ayumu-bekki/B-Fox/bfox_receiver/main/logger.cc

// ESP32 B-Fox Receiver
// (C)2025 bekki.jp

// Include ----------------------
#include "logger.h"

namespace bfox_receiver_system {
namespace logger {

void InitializeLogLevel() {
#if CONFIG_DEBUG != 0
  esp_log_level_set("*", ESP_LOG_INFO);
  esp_log_level_set(kTag, ESP_LOG_VERBOSE);
  ESP_LOGD(kTag, "DEBUG MODE");
#else
  esp_log_level_set("*", ESP_LOG_WARN);
  esp_log_level_set(kTag, ESP_LOG_INFO);
#endif
}

}  // namespace logger
}  // namespace bfox_receiver_system
