ayumu-bekki/B-Fox/bfox_receiver/main/logger.h

#ifndef BFOX_RECEIVER_MAIN_LOGGER_H_
#define BFOX_RECEIVER_MAIN_LOGGER_H_
// ESP32 B-Fox Receiver
// (C)2025 bekki.jp

// Include ----------------------
#include <esp_log.h>

// systen Loglevel Redefine
#undef LOG_LOCAL_LEVEL
#define LOG_LOCAL_LEVEL ESP_LOG_VERBOSE

namespace bfox_receiver_system {

/// Application Log Tag
static constexpr char kTag[] = "BFoxReceiver";

namespace logger {

void InitializeLogLevel();

}  // namespace logger
}  // namespace bfox_receiver_system

#endif  // BFOX_RECEIVER_MAIN_LOGGER_H_
